JonasCz/DomesdayDuplicator-audio-ADC/Linux-Application/DomesdayDuplicator/mainwindow.h

/************************************************************************

    mainwindow.h

    Capture application for the Domesday Duplicator
    DomesdayDuplicator - LaserDisc RF sampler
    Copyright (C) 2018-2019 Simon Inns

    This file is part of Domesday Duplicator.

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
    Email: simon.inns@gmail.com

************************************************************************/
#pragma once
#include <QMainWindow>
#include <QLabel>
#include <QDate>
#include <QTimer>
#include <QMessageBox>
#include "aboutdialog.h"
#include "configurationdialog.h"
#include "configuration.h"
#include "UsbDeviceBase.h"
#include "playercommunication.h"
#include "playercontrol.h"
#include "playerremotedialog.h"
#include "automaticcapturedialog.h"
#include "advancednamingdialog.h"
#include "amplitudemeasurement.h"
#include "ILogger.h"
#include <chrono>
#include <filesystem>
#include <optional>
#include <memory>

namespace Ui {
class MainWindow;
}

class MainWindow : public QMainWindow
{
    Q_OBJECT

public:
    explicit MainWindow(const ILogger& log, QWidget *parent = nullptr);
    ~MainWindow();

private slots:
    void configurationChangedSignalHandler();
    void remoteControlCommandSignalHandler(PlayerRemoteDialog::RemoteButtons button);
    void remoteControlSearchSignalHandler(qint32 position, PlayerRemoteDialog::PositionMode positionMode);
    void remoteControlManualSerialCommandHandler(QString commandString);
    void remoteControlReadUserCodesCommandHandler();
    void startAutomaticCaptureDialogSignalHandler(AutomaticCaptureDialog::CaptureType captureType,
                                                              qint32 startAddress, qint32 endAddress,
                                                              AutomaticCaptureDialog::DiscType discTypeParam);
    void stopAutomaticCaptureDialogSignalHandler();
    void updateAutomaticCaptureStatus();
    void automaticCaptureCompleteSignalHandler(bool success);

    void playerConnectedSignalHandler();
    void playerDisconnectedSignalHandler();

    void startCaptureSignalHandler();
    void stopCaptureSignalHandler();

    void updateCaptureStatus();
    void updateDeviceStatus();
    void updatePlayerControlInformation();
    void updateStorageInformation();
    void updateAmplitudeDataBuffer();
    void updateAmplitudeLabel();
    void updateAudioAmplitudeLabel();

    void on_actionExit_triggered();
    void on_actionTest_mode_toggled(bool arg1);
    void on_actionAbout_triggered();
    void on_actionPreferences_triggered();
    void on_capturePushButton_clicked();
    void on_actionPlayer_remote_triggered();
    void on_actionAutomatic_capture_triggered();
    void on_limitDurationCheckBox_stateChanged(int arg1);
    void on_stopCaptureOnAmplitudeDropCheckBox_stateChanged(int arg1);
    void on_actionAdvanced_naming_triggered();

private:
    struct AmplitudeRecord
    {
        std::chrono::time_point<std::chrono::steady_clock> sampleTime;
        double amplitude;
    };
    struct TimeCodeRecord
    {
        std::chrono::time_point<std::chrono::steady_clock> sampleTime;
        qint32 timeCodeOrFrameNumber;
        bool inLeadIn;
        bool inLeadOut;
    };
    struct PlayerStatusRecord
    {
        std::chrono::time_point<std::chrono::steady_clock> sampleTime;
        PlayerCommunication::PlayerState playerState;
    };
    struct PhysicalPositionRecord
    {
        std::chrono::time_point<std::chrono::steady_clock> sampleTime;
        float physicalPosition;
    };

private:
    void RefreshControlVisibility();
    void StopCapture();
    void StartCapture();

private:
    const ILogger& log;
    std::unique_ptr<Configuration> configuration;
    std::unique_ptr<UsbDeviceBase> usbDevice;
    std::unique_ptr<QLabel> usbStatusLabel;
    std::unique_ptr<QStorageInfo> storageInfo;

    std::unique_ptr<Ui::MainWindow> ui;
    std::unique_ptr<AboutDialog> aboutDialog;
    std::unique_ptr<AutomaticCaptureDialog> automaticCaptureDialog;
    std::unique_ptr<ConfigurationDialog> configurationDialog;
    std::unique_ptr<PlayerRemoteDialog> playerRemoteDialog;
    std::unique_ptr<PlayerControl> playerControl;
    std::unique_ptr<AdvancedNamingDialog> advancedNamingDialog;

    std::atomic<bool> isCaptureRunning = false;
    bool isCaptureStopping = false;
    bool playerStopRequested = false;
    std::filesystem::path captureFilePath;
    std::unique_ptr<QTimer> captureStatusUpdateTimer;
    std::unique_ptr<QTimer> playerControlTimer;
    std::unique_ptr<QTimer> deviceStatusTimer;
    std::unique_ptr<QTimer> automaticCaptureTimer;
    std::unique_ptr<QTimer> storageInfoTimer;
    std::unique_ptr<QTimer> amplitudeTimer;
    std::chrono::time_point<std::chrono::steady_clock> captureStartTime;
    std::chrono::time_point<std::chrono::steady_clock> captureEndTime;
    std::vector<AmplitudeRecord> amplitudeRecord;
    std::vector<TimeCodeRecord> playerTimeCodeRecord;
    std::vector<PlayerStatusRecord> playerStatusRecord;
    std::vector<PhysicalPositionRecord> playerPhysicalPositionRecord;

    bool isPlayerConnected = false;
    bool usbDevicePresentLastCheck = false;
    bool isPlayerConnectedLastCheck = false;
    PlayerCommunication::DiscType playerDiscTypeCached = PlayerCommunication::DiscType::unknownDiscType;
    std::optional<QString> playerDiscStatusCached;
    std::optional<QString> playerStandardUserCodeCached;
    std::optional<QString> playerPioneerUserCodeCached;
    qint32 minPlayerTimeCode = -1;
    qint32 maxPlayerTimeCode = -1;
    qint32 minPlayerFrameNumber = -1;
    qint32 maxPlayerFrameNumber = -1;
    float minPlayerPhysicalPosition = -1;
    float maxPlayerPhysicalPosition = -1;

    // Saved disk naming/notes metadata
    std::optional<QString> namingDiskTitle;
    std::optional<bool> namingDiskIsCav;
    std::optional<bool> namingDiskIsNtsc;
    std::optional<int> namingDiskSide;
    std::optional<AdvancedNamingDialog::AudioType> namingDiskAudioType;
    std::optional<QString> namingDiskMintMarks;
    std::optional<QString> namingDiskNotes;
    std::optional<QString> namingDiskMetadataNotes;

    // Remote control states
    PlayerCommunication::DisplayState remoteDisplayState;
    PlayerCommunication::AudioState remoteAudioState;
    qint32 remoteSpeed;
    PlayerCommunication::ChapterFrameMode remoteChapterFrameMode;

    // Amplitude drop tracking for auto-stop
    std::optional<std::chrono::time_point<std::chrono::steady_clock>> amplitudeDropStartTime;

    void startPlayerControl();
    void updatePlayerRemoteDialog();
    void updateAmplitudeUI();
    void checkAmplitudeDropStop();
};
